nekoewen/titan-keyboard/pcb/1.jpg

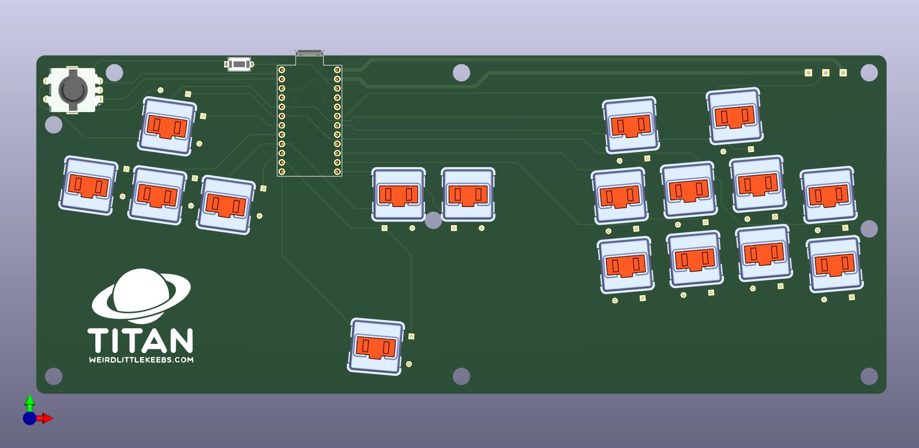
pcb/1.jpg
