nekoewen/titan-keyboard/pcb/2.jpg

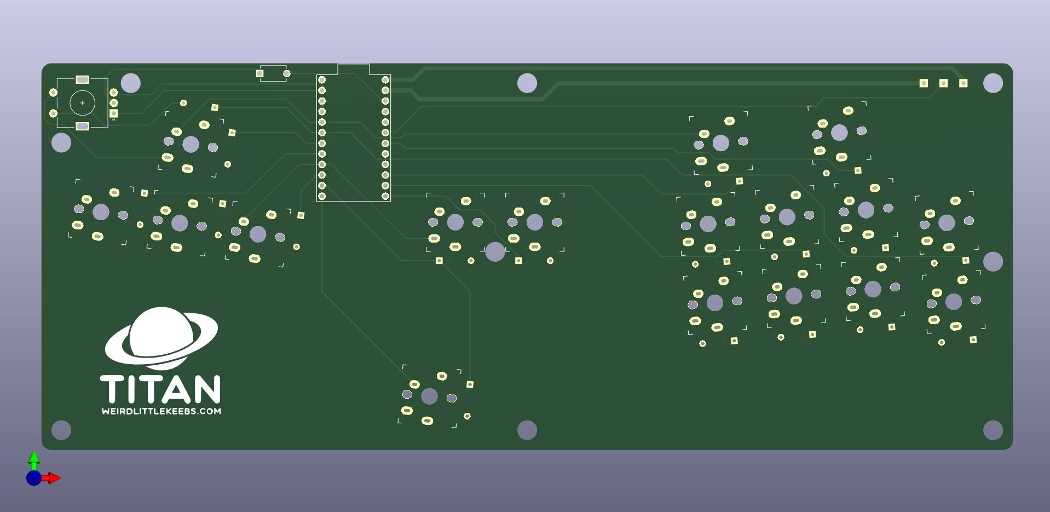
pcb/2.jpg
