nekoewen/titan-keyboard/pcb/3.jpg

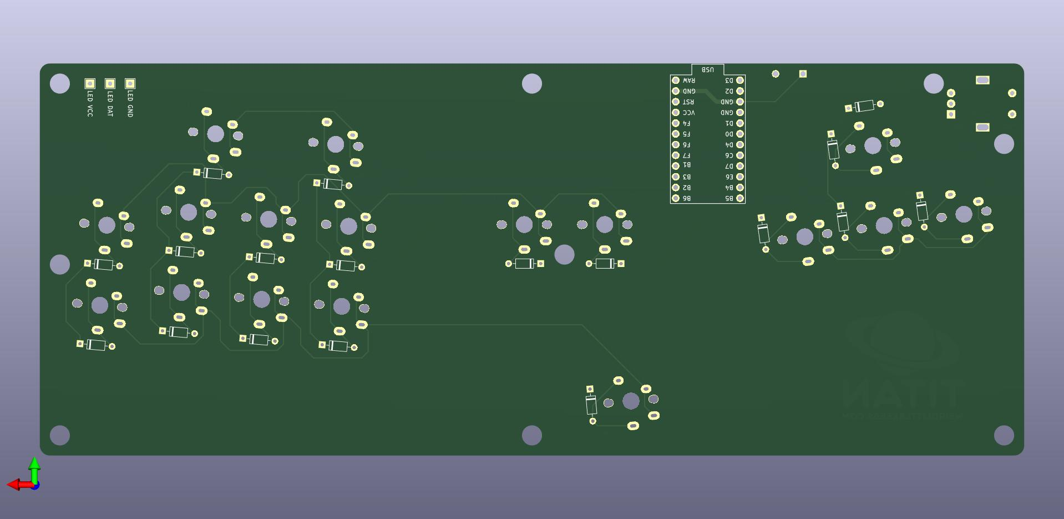
pcb/3.jpg
