nekoewen/titan-keyboard/pcb/4.jpg

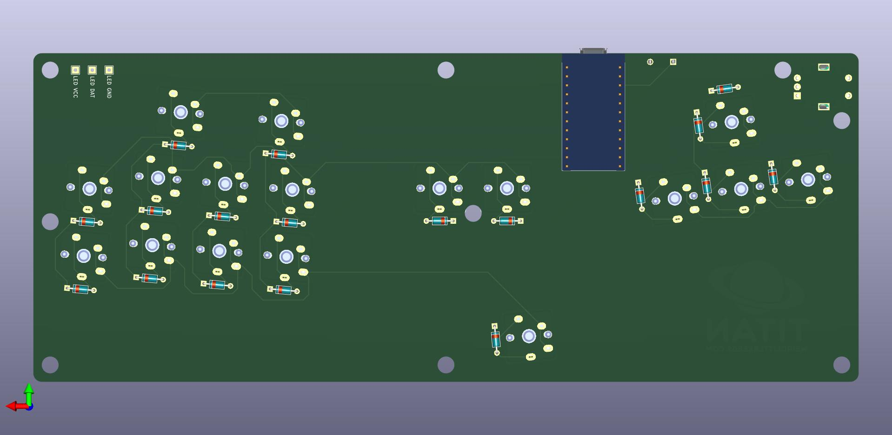
pcb/4.jpg
