nekoewen/titan-keyboard/pcb/5.jpg

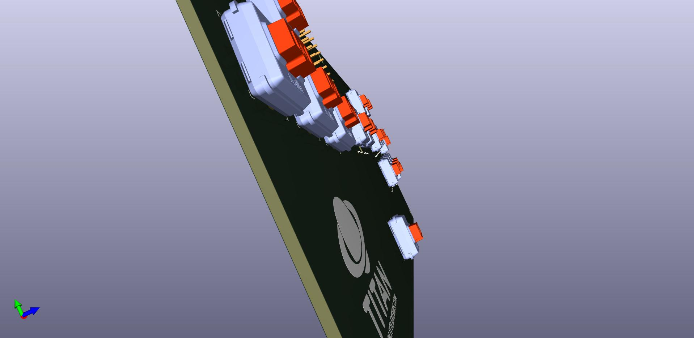
pcb/5.jpg
