nekoewen/titan-keyboard/pcb/6.jpg

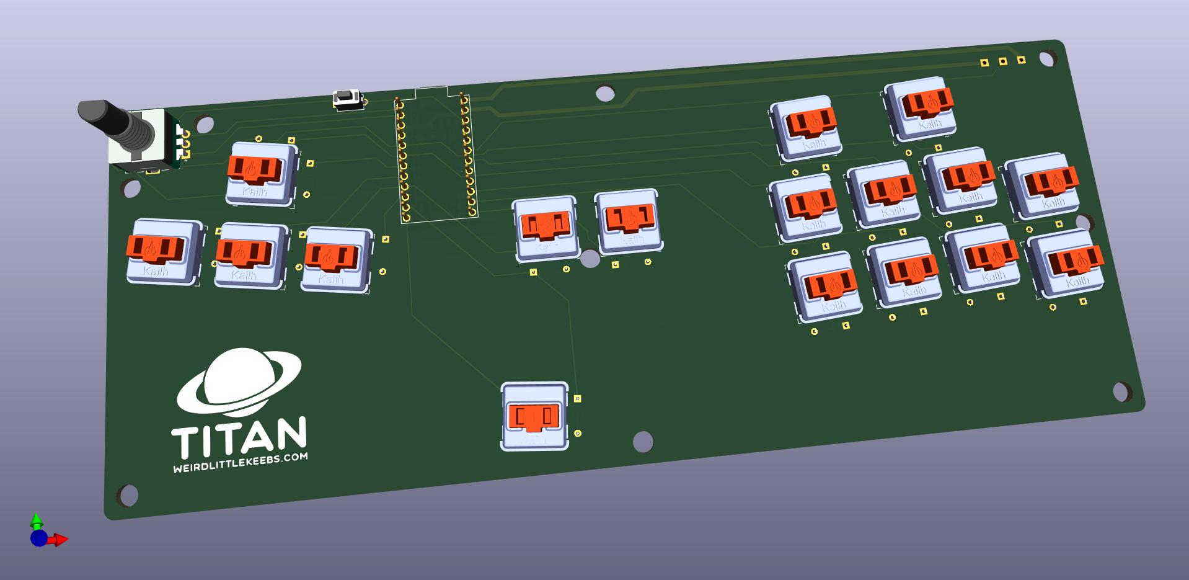
pcb/6.jpg
