nekoewen/titan-keyboard/pcb/7.jpg

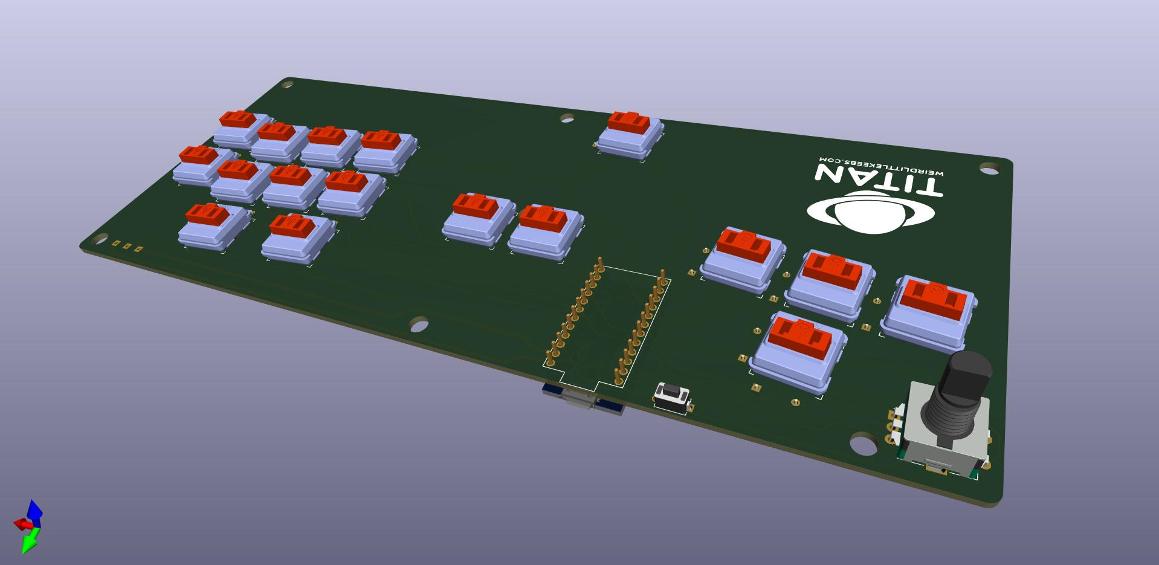
pcb/7.jpg
