nekoewen/titan-keyboard/pcb/8.jpg

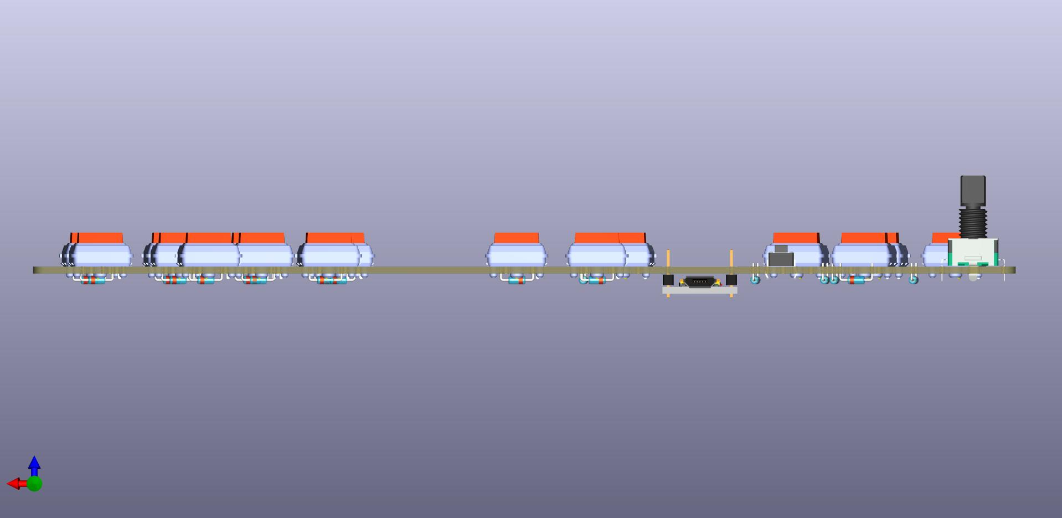
pcb/8.jpg
