nekoewen/titan-keyboard/pcb/9.jpg

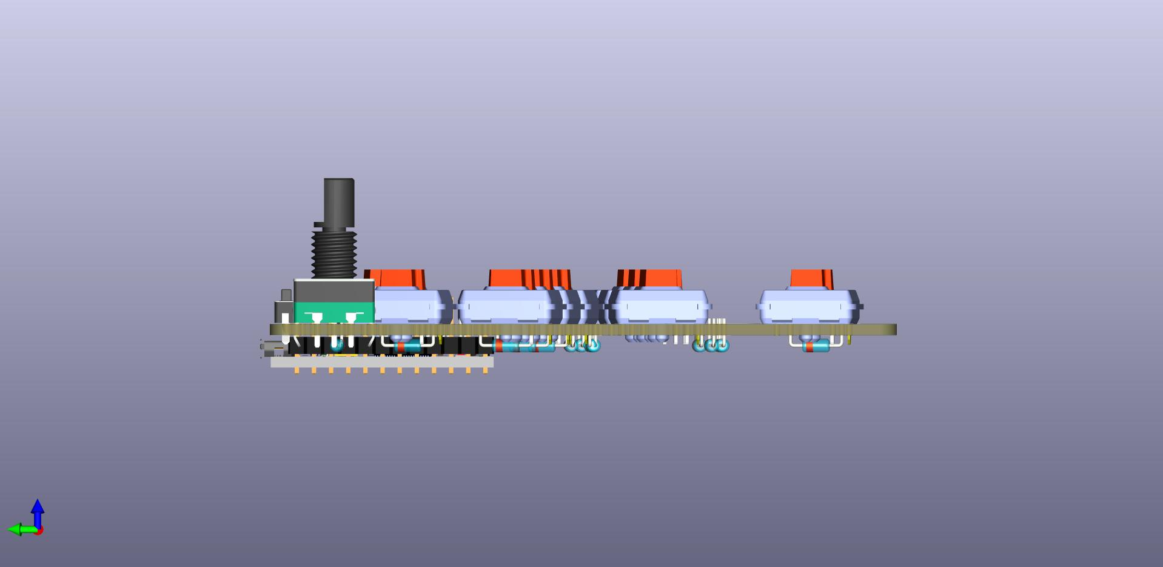
pcb/9.jpg
